Etiene/BMONS/doc/RapportFinal/images/choixArduino.pdf

carte | ADC | nb pin | GSM | processeur | prix | Avantages | Inconvénients
APF28 | 2MHz | 2x80 | Apw | 454MHz | 55 €+ 164€(apw) | ADC rapide | Soudures a effectuer
arduino Mega | 10 kHz | 55(gpio) 16(analog) | shield (57€) | 16MHz | 58€ +57€(shield) | librairie fft disponible | pas de GPS avec ce shield
arduino Due | 1MHz | 54 gpio 12 analog | shield(57€) | 64MHz | 49€+57€(shield) | ADC rapide | pas de librairie fft
netduino | 30MHz | 6 analog 22 gpio | intégré | 120MHz | 30 € | TCP/IP déjà integré ADC rapide | pas commun, 0°C mini, timming?, besoin de beaucoup de memoire
