Etiene/BMONS/doc/RapportFinal/images/specif_comp.pdf

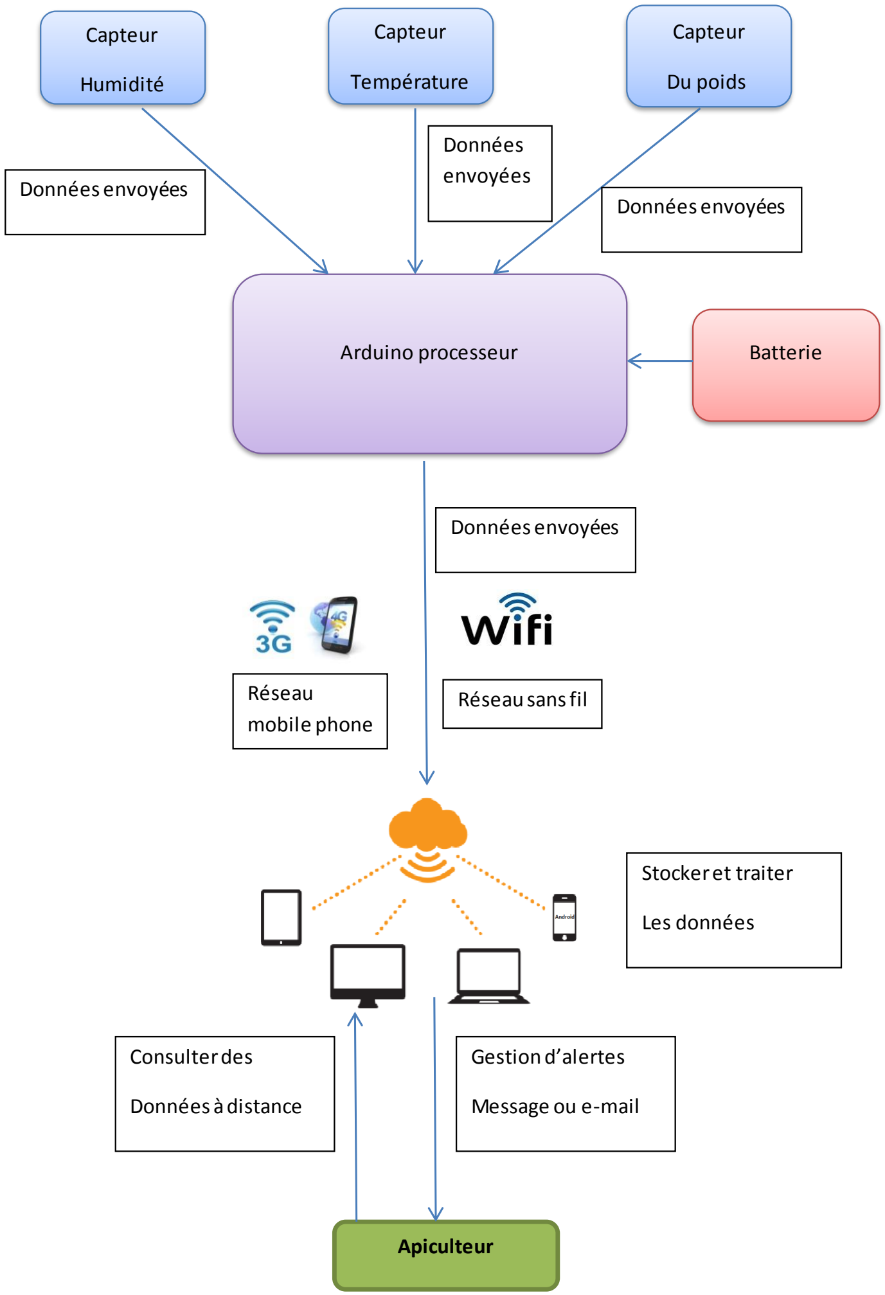
[picture p31: figure]
Capteur; Température; Humidité; Du poids; Apiculteur; Gestion d’alertes; Message ou e-mail; Arduino processeur; Réseau; Réseau sans fil; mobile phone; Données envoyées; Stocker et traiter; Les données; Consulter des; Données à distance; Batterie

Capteur

Système
embarqué

Réseau de
transmission
des données

Utilisateurs

Serveur
