Etiene/BMONS/doc/RapportFinal/images/axeData2.pdf

Bee_Monitor | Alerte Météorologique

Forte pluie, température
inhabituelle (vent ?) qui affectent l'activité/la production
Sources | Requete | Type info
Serveur | Accéder aux données décrivant l'état de sa ruche | Données/Alertes
Sources | Evènement | Element(s) concernés | Remarques
Bee_monitor | Alerte Capteurs endomagés ou mauvaises saisies des données | Ensemble des capteurs | Pour repérer: fortes variations ou valeurs hors intervalles prévus
Sources | Requete | Type info
Serveur | Accéder aux données décrivant l'état de sa ruche | Données/Alertes
Serveur | Configurer | Données/Alertes
Sources | Evènement
Capteur d'inclinaison | Renversement de la ruche
Bee_monitor | Alerte Ruche renversée
Capteur d'ouverture | Couvercle mal placé ou tombé
Bee_monitor | Alerte Ruche ouverte

Transmettre des messages

Alerter l'apiculteur

### FS3: Résister à l'environnement extérieur

Transmettre des messages

Alerter l'apiculteur

### FC2: Résister à l'environement de la ruche
