Etiene/BMONS/doc/RapportFinal/images/axeData3.pdf

Capteur d'inclinaison | Renversement de la ruche
Bee_monitor | Alerte La ruche a subit un choc
Capteur d'humidité | Infiltration/problèmes d'étanchéité
Bee_monitor | Alerte Ruche exposée à l'humidité
Balance | Déplacement de la ruche non prévu
Bee_monitor | Alerte Ruche déplacée
Sources | Data | Unité
Panneaux solaires/Eoliennes | Luminosité reçue/vitesse du vent | Lux-m/s
Batteries du bee_monitor | Energie disponible et consommation | J
Sources | Requete | Type info
Serveur | Accéder aux données décrivant l'état de sa ruche | Données des batteries/Autonomie/Alertes
Serveur | Configurer | Données des batteries/Alertes
Sources | Evènement
Bee_monitor | Alerte Etat des batteries faible

### FS4: Etre autonome en énergie

Alerter l'apiculteur

Transmettre des messages
