Etiene/BMONS/doc/RapportFinal/images/Exigences3.pdf

Transmettre les données par ondes radio | 3G ou 4G

Pouvoir stocker les données localement

Déclancher des mesures à intervalles réguliers

exi met 6 | detecter l'essaimage | Avertir l'apiculteur en cas de détection d'essaimage
| | Mesurer le poids de la ruche | [0 ; 150] résolution 100g fréquence 1/heure
| | Transmettre les données par ondes radio | 3G ou 4G
| | pouvoir stocker les données localement
| | Déclancher des mesures à intervalles réguliers
| | detecter les renversements
| | detecter l'ouverture de la ruche
| | donner la position de la ruche
| | Avertir l'apiculteur en cas de choc
| | Détecter la position de la ruche
| | Transmettre les données par ondes radio | 3G ou 4G
| | Pouvoir stocker les données localement

exi met 7

veiller à la
sécurité de la
ruche

exi met 5

detecter les
premise de
l'essaimage
