Etiene/BMONS/doc/RapportFinal/images/BeteACornesBMONS.pdf

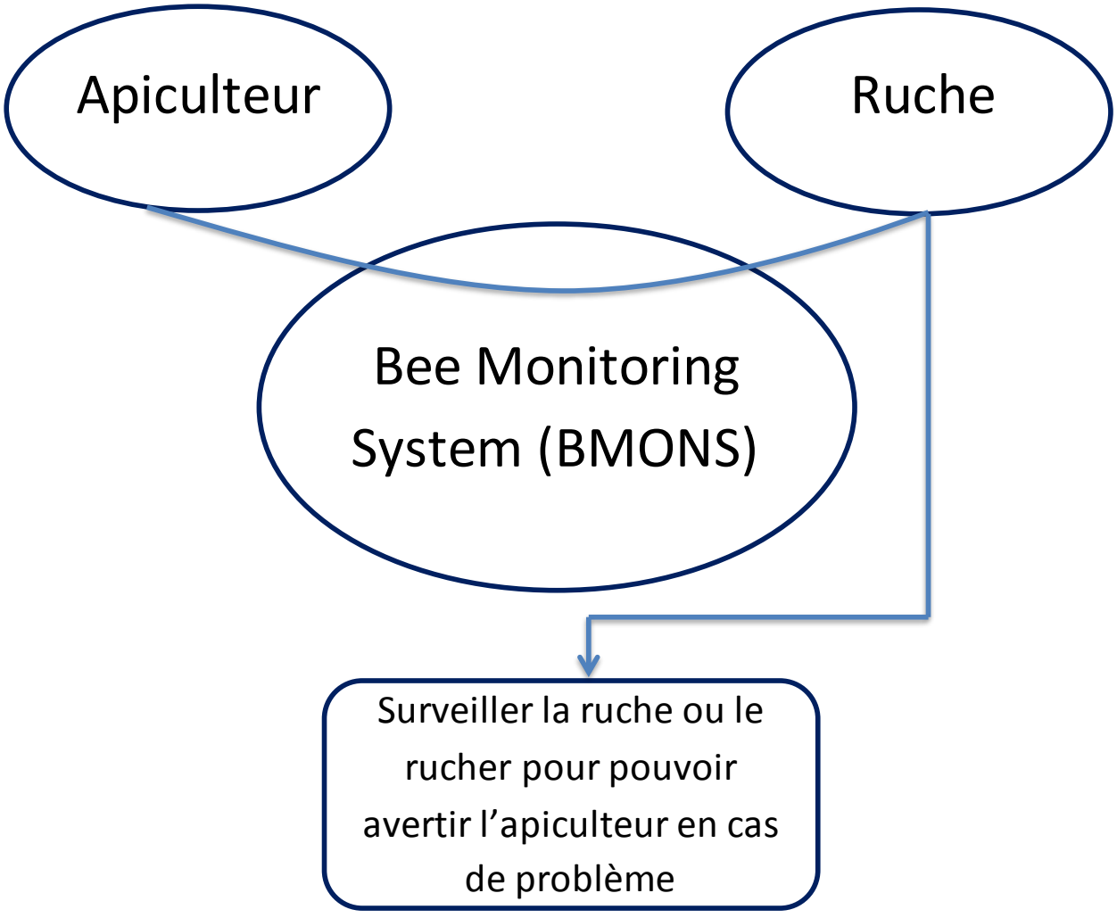
[picture p115: figure]
Surveiller la ruche ou le rucher pour pouvoir avertir l’apiculteur en cas de problème; Ruche; Bee Monitoring System (BMONS); Apiculteur
