Etiene/BMONS/doc/RapportFinal/images/diagpieuvre.pdf

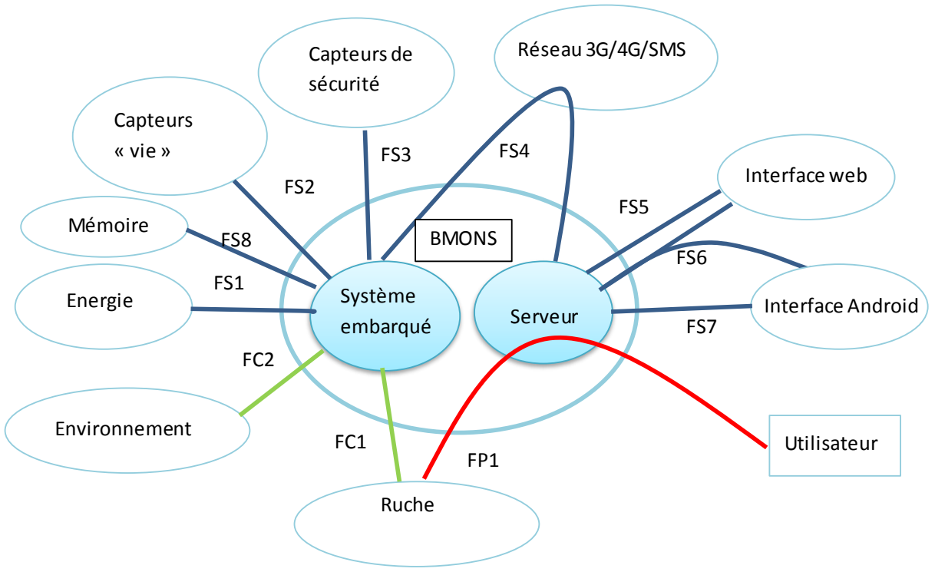
[picture p116: figure]
Capteurs de sécurité; Energie; Environnement; Utilisateur; Interface web; Capteurs « vie »; Réseau 3G/4G/SMS; Système; embarqué; Serveur; Ruche; BMONS; Interface Android; Mémoire

FP1 : Informer l’apiculteur de l’état de la ruche

FC1 : Etre adapté aux dimensions de la ruche FC2 : Résister à l’environnement de la ruche

FS1 : Etre autonome en énergie
FS2 : Acquérir les données relatives à la vie de la ruche
FS3 : Acquérir les données relatives à l’intégrité de la ruche FS4 : Communiquer avec le serveur via le réseau 3G/4G/SMS FS5 : Proposer une IHM web
FS6 : Proposer un accès via l’API
FS7 : Proposer une IHM Android
FS8 : Conserver les données localement
