Etiene/BMONS/doc/FAST.png

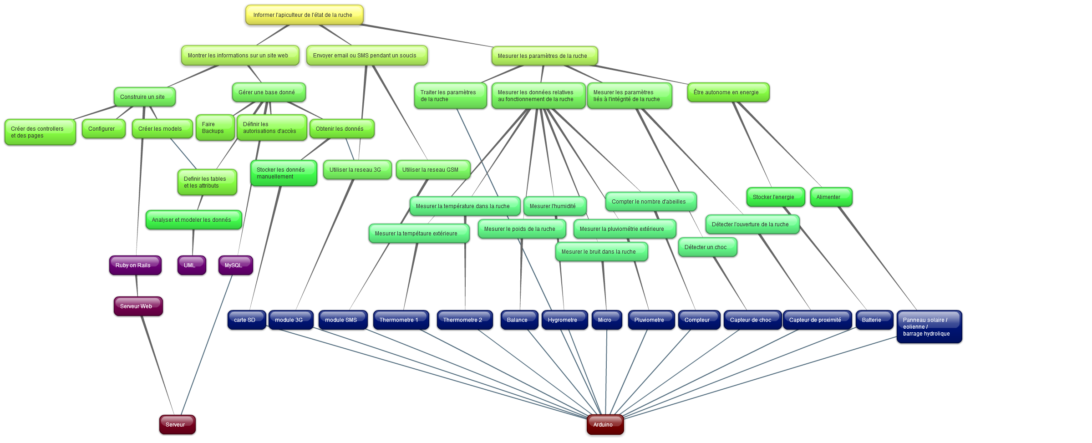
doc/FAST.png
