Etiene/BMONS/doc/Modèle Base de données/digClass.png

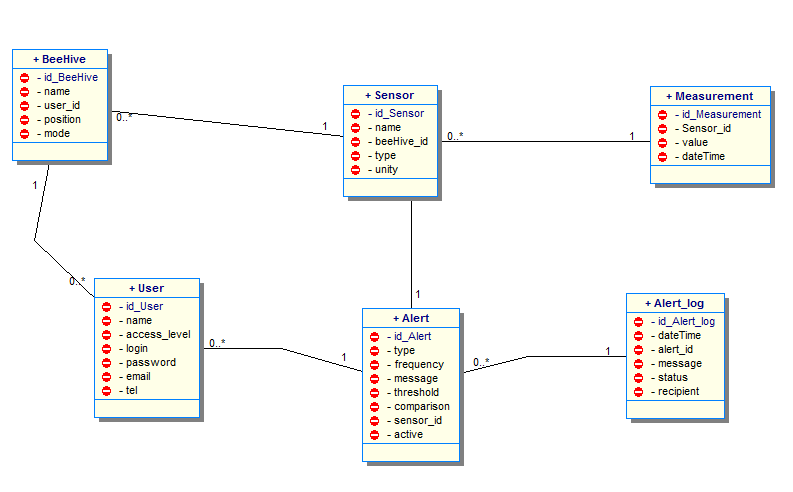
doc/Modèle Base de données/digClass.png
