Etiene/BMONS/doc/Modèle Base de données/mcd.png

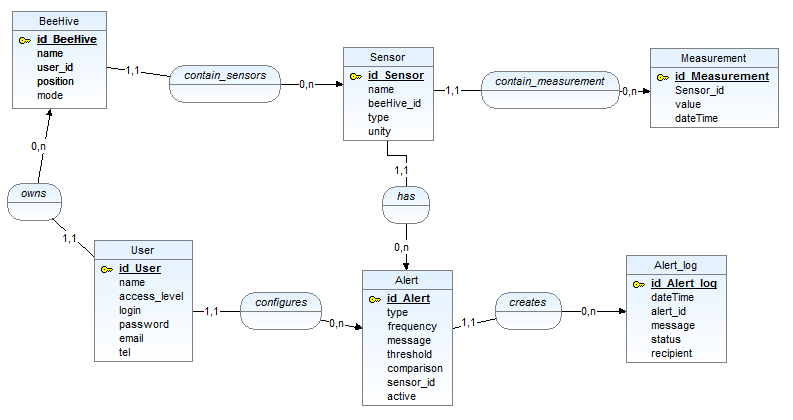
doc/Modèle Base de données/mcd.png
