Etiene/BMONS/doc/Modèle Base de données/MLD.png

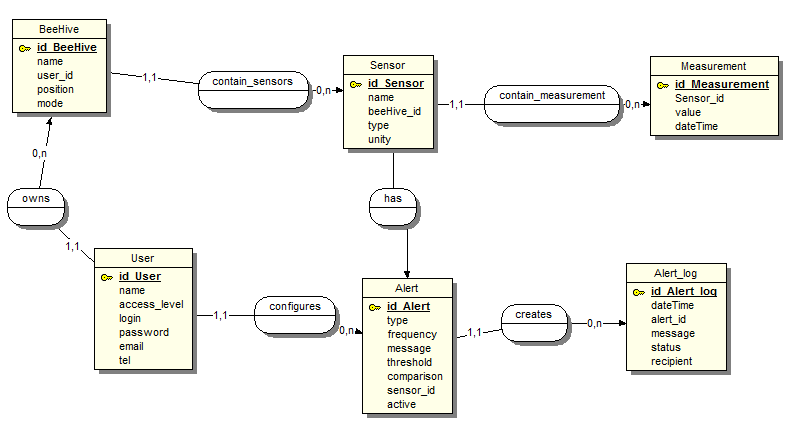
doc/Modèle Base de données/MLD.png
