Etiene/BMONS/doc/RapportFinal/images/arnia2.jpg

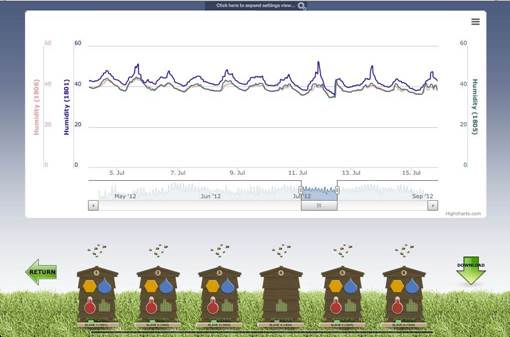
doc/RapportFinal/images/arnia2.jpg
