Etiene/BMONS/doc/RapportFinal/images/GANTT2.png

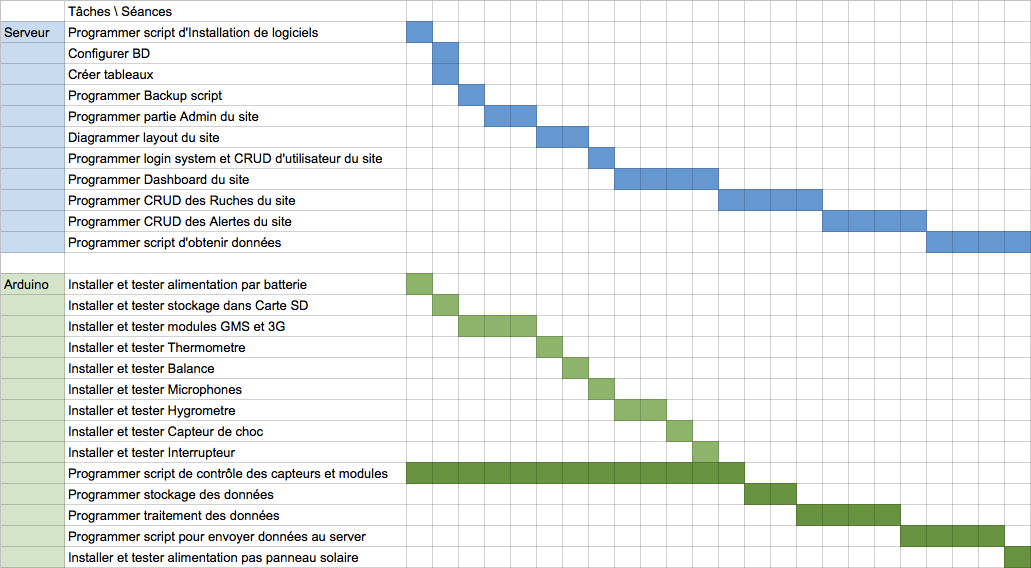
doc/RapportFinal/images/GANTT2.png
