Etiene/BMONS/doc/RapportFinal/images/GANTT.png

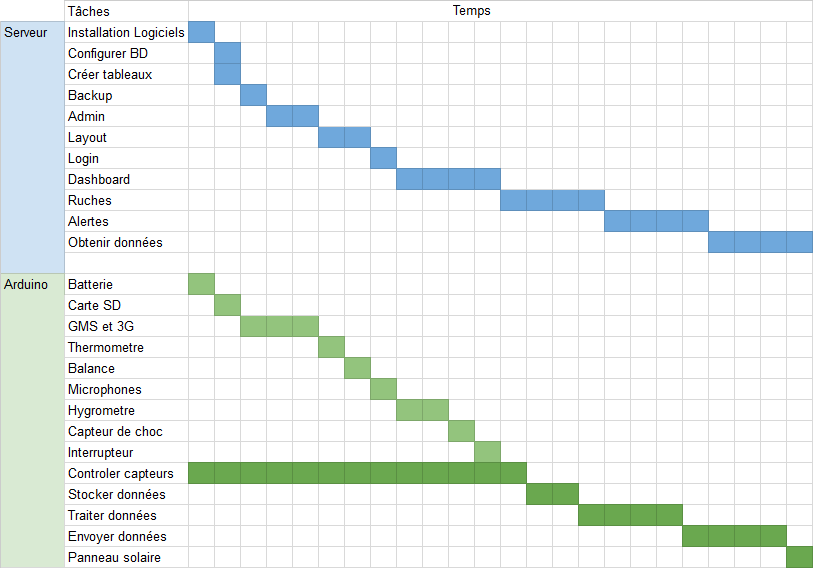
doc/RapportFinal/images/GANTT.png
