Etiene/BMONS/doc/RapportFinal/images/WBS2.png

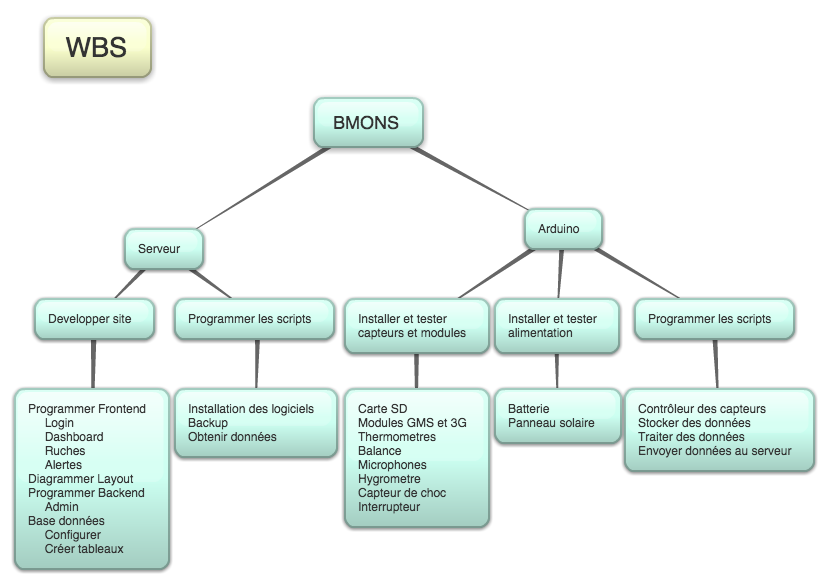
doc/RapportFinal/images/WBS2.png
