Etiene/BMONS/doc/UseCaseDiagram1.jpg

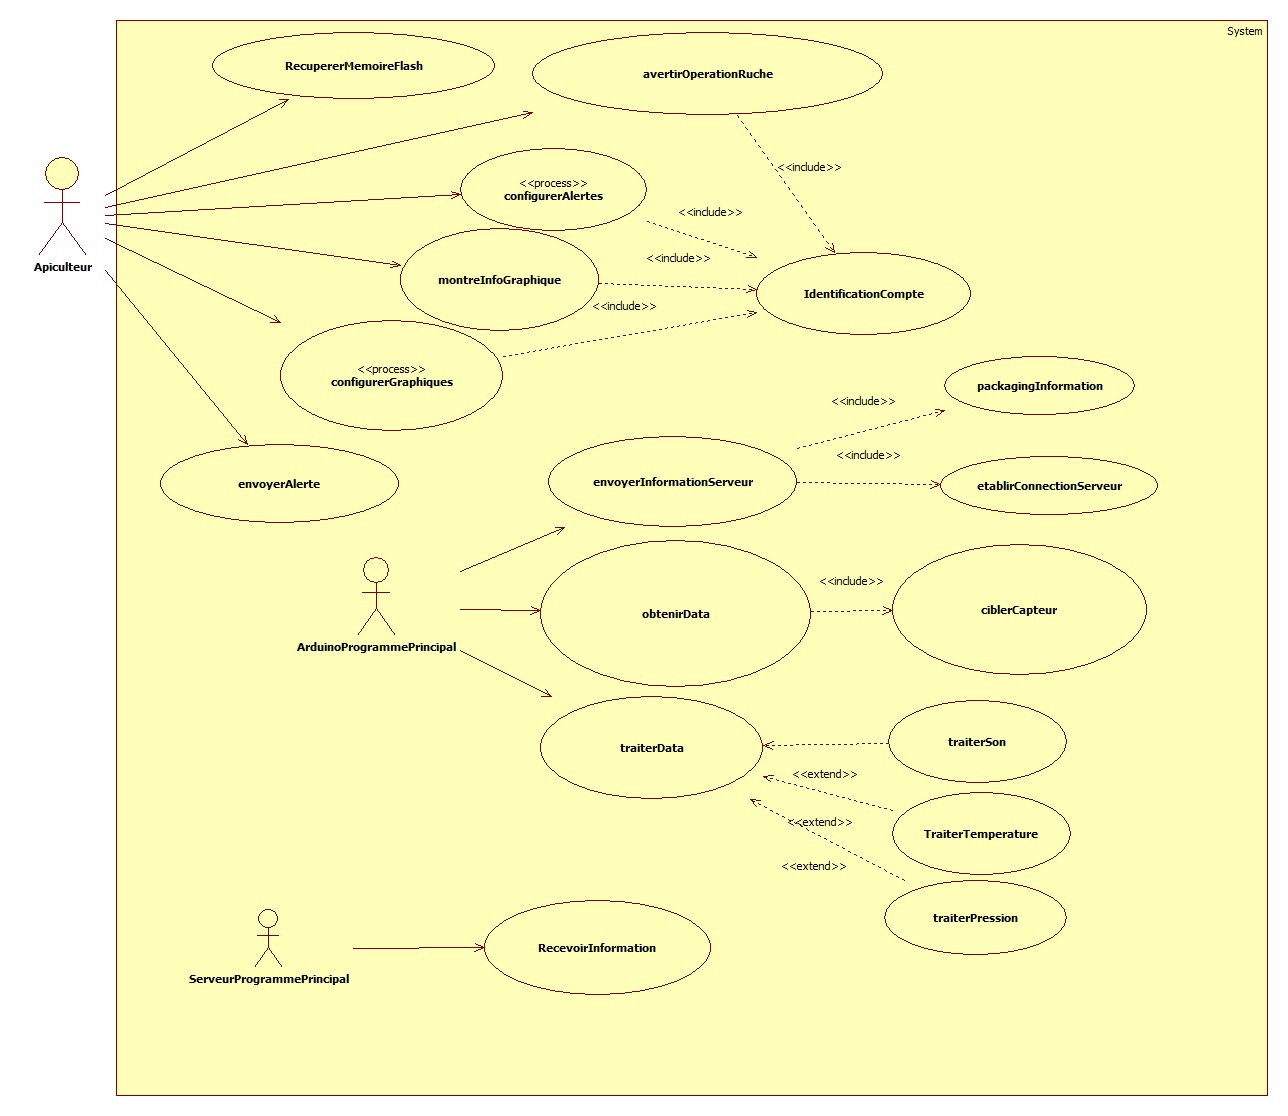
doc/UseCaseDiagram1.jpg
