Etiene/BMONS/doc/UseCaseDiagram2.jpg

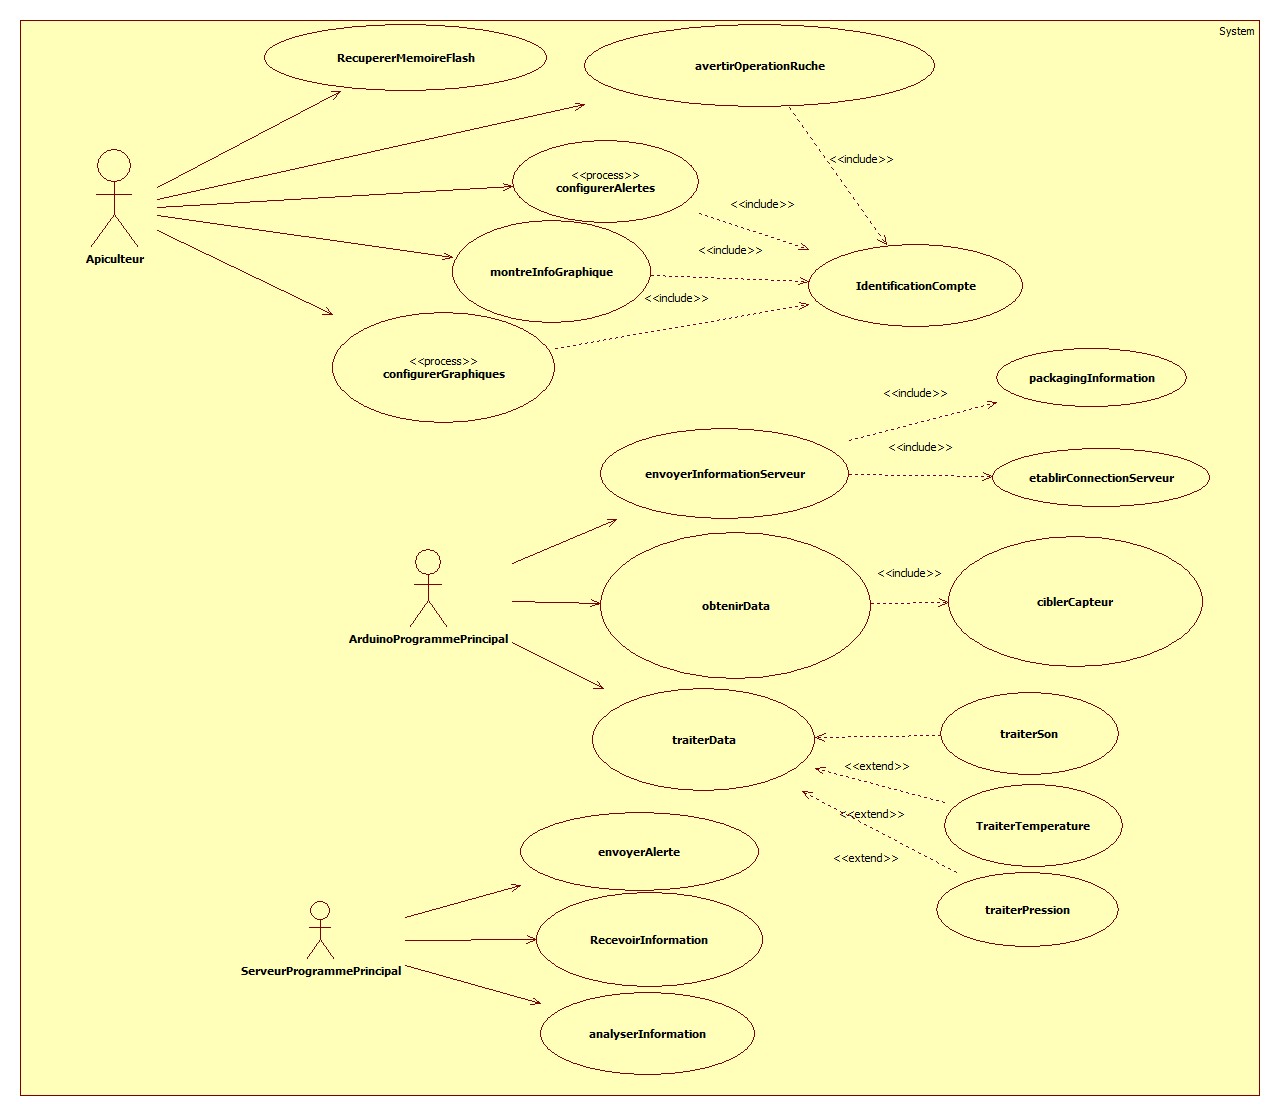
doc/UseCaseDiagram2.jpg
