Etiene/BMONS/doc/RapportFinal/images/ExempleCarnetDeBord.PNG

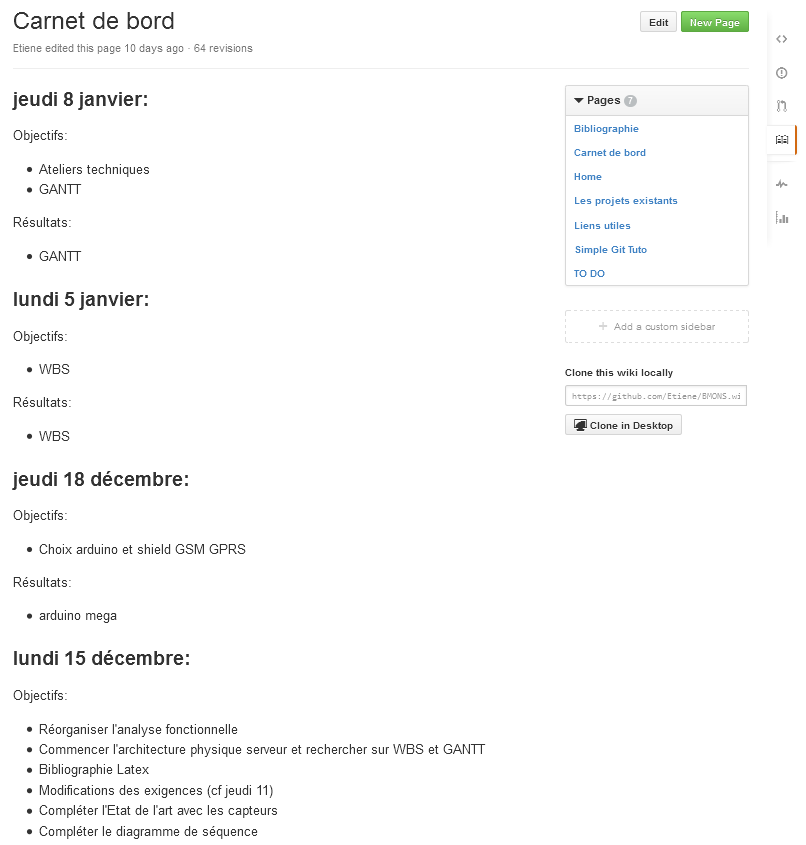
doc/RapportFinal/images/ExempleCarnetDeBord.PNG
