Etiene/BMONS/doc/RapportFinal/images/analyseFonctionelle1.pdf

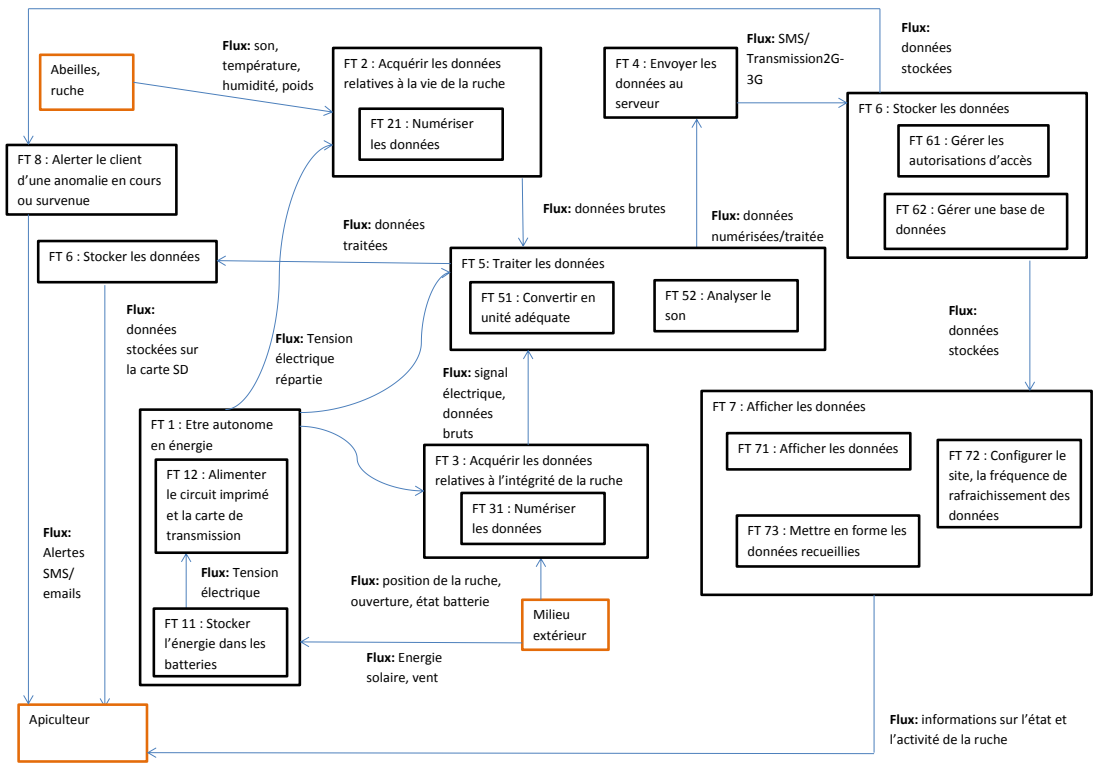
[picture p143: page 1]
Flux: Tension électrique répartie; Flux: Tension électrique; Flux: données stockées; Flux: SMS/ Transmission2G- 3G; Flux: données numérisées/traitée; Flux: son, température, humidité, poids; Flux: données traitées; Milieu extérieur; Apiculteur; Abeilles, ruche; Flux: Energie solaire, vent; FT 21 : Numériser les données; Flux: Alertes SMS/ emails; FT 31 : Numériser les données

FT 2 : Acquérir les données
relatives à la vie de la ruche

FT 4 : Envoyer les
données au
serveur

FT 6 : Stocker les données

FT 61 : Gérer les
autorisations d’accès

FT 8 : Alerter le client
d’une anomalie en cours
ou survenue

Flux: données brutes

FT 62 : Gérer une base de
données

FT 5: Traiter les données

FT 51 : Convertir en
unité adéquate

FT 52 : Analyser le
son

Flux:
stockées sur
la carte SD

Flux: signal
électrique,
bruts
FT 3 : Acquérir les données
relatives à l’intégrité de la ruche

FT 7 : Afficher les données

FT 1 : Etre autonome
en énergie

FT 71 : Afficher les données

FT 72 : Configurer le
site, la fréquence de
rafraichissement des

FT 12 : Alimenter
le circuit imprimé
et la carte de
transmission

FT 73 : Mettre en forme les
données recueillies

Flux: position de la ruche,
ouverture, état batterie

FT 11 : Stocker
l’énergie dans les
batteries

Flux: informations sur l’état et
l’activité de la ruche
