Etiene/BMONS/doc/RapportFinal/images/analyseFonctionelle.pdf

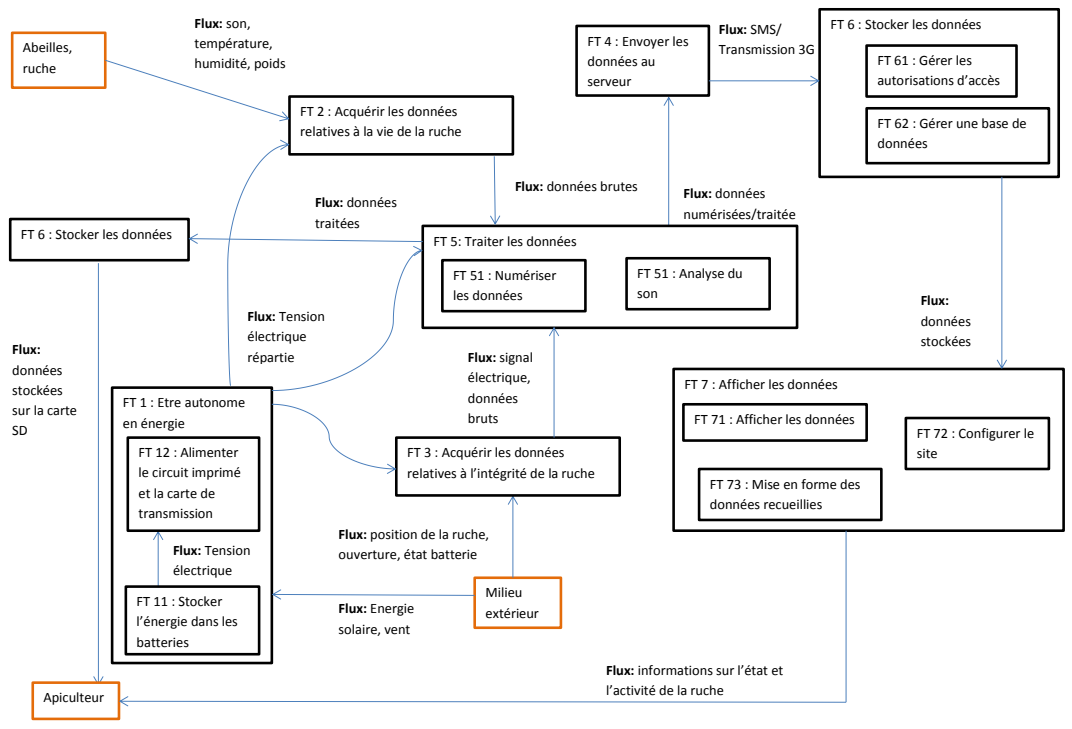
[picture p144: page 1]
Flux: Tension électrique; Flux: données stockées; Flux: SMS/ Transmission 3G; Flux: données numérisées/traitée; Flux: signal électrique, données bruts; Flux: son, température, humidité, poids; Flux: données traitées; Milieu extérieur; Apiculteur; Abeilles, ruche; Flux: Energie solaire, vent; FT 51 : Numériser les données

FT 6 : Stocker les données

FT 4 : Envoyer les
données au
serveur

FT 61 : Gérer les
autorisations d’accès

FT 2 : Acquérir les données
relatives à la vie de la ruche

FT 62 : Gérer une base de
données

Flux: données brutes

FT 5: Traiter les données

FT 51 : Analyse du
son

répartie Flux:
stockées
sur la carte

FT 7 : Afficher les données

FT 1 : Etre autonome
en énergie

FT 71 : Afficher les données

FT 72 : Configurer le
site

FT 12 : Alimenter
le circuit imprimé
et la carte de
transmission

FT 3 : Acquérir les données
relatives à l’intégrité de la ruche

FT 73 : Mise en forme des
données recueillies

Flux: position de la ruche,
ouverture, état batterie

FT 11 : Stocker
l’énergie dans les
batteries

Flux: informations sur l’état et
l’activité de la ruche
