Etiene/BMONS/doc/Fast_BMONS.pdf

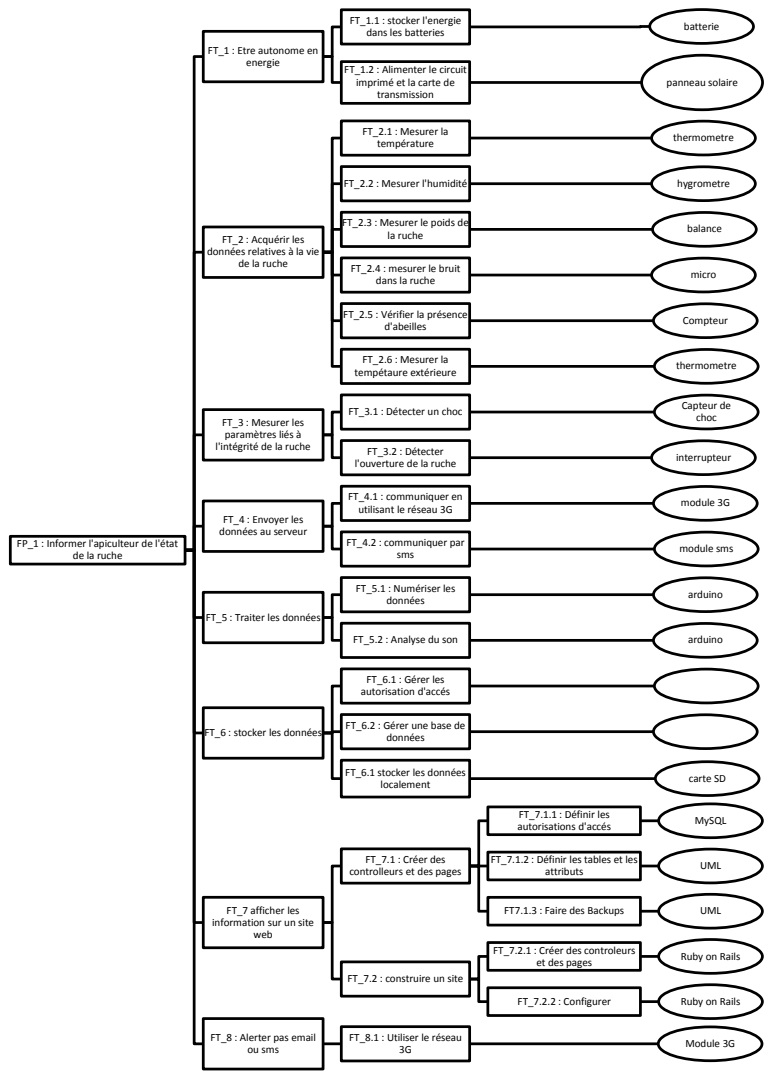
[picture p145: page 1]
energie; FT_1.1 : stocker l'energie; dans les batteries; batterie; panneau solaire; FT_2.1 : Mesurer la; température; thermometre; FT_2.2 : Mesurer l'humidité; hygrometre; la ruche; balance; dans la ruche; micro; d'abeilles; Compteur; FT_2.6 : Mesurer la; tempétaure extérieure; FT_3.1 : Détecter un choc; Capteur de; choc; FT_3.2 : Détecter; l'ouverture de la ruche; interrupteur; FT_4.1 : communiquer en; utilisant le réseau 3G; module 3G; FT_4.2 : communiquer par sms; module sms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

FT_1 : Etre autonome en

FT_1.2 : Alimenter le circuit
imprimé et la carte de
transmission

FT_2.3 : Mesurer le poids de

FT_2 : Acquérir les
données relatives à la vie
de la ruche

FT_2.4 : mesurer le bruit

FT_2.5 : Vérifier la présence

FT_3 : Mesurer les
paramètres liés à
l'intégrité de la ruche

FT_4 : Envoyer les
données au serveur

FP_1 : Informer l'apiculteur de l'état

FT_5 : Traiter les données

FT_6.2 : Gérer une base de

FT_6 : stocker les données

FT_6.1 stocker les données

FT_7.1 : Créer des
controlleurs et des pages

FT_7.1.2 : Définir les tables et les

FT_7 afficher les
information sur un site

FT_7.2.1 : Créer des controleurs

FT_7.2 : construire un site

FT_8 : Alerter pas email

FT_8.1 : Utiliser le réseau
