Etiene/BMONS/bmons-site/test/fixtures/measurements.yml

# Read about fixtures at http://api.rubyonrails.org/classes/ActiveRecord/FixtureSet.html

#TEMPERATURE RUCHE 1
one:
  value: 15
  datetime: 2015-02-17 17:05:09
  sensor_id: 1

two:
  value: 15.1
  datetime: 2015-02-17 17:15:09
  sensor_id: 1

three:
  value: 15.2
  datetime: 2015-02-17 17:25:09
  sensor_id: 1

four:
  value: 15.3
  datetime: 2015-02-17 17:35:09
  sensor_id: 1

five:
  value: 16
  datetime: 2015-02-17 17:45:09
  sensor_id: 1

six:
  value: 15.3
  datetime: 2015-02-17 17:55:09
  sensor_id: 1

seven:
  value: 15
  datetime: 2015-02-17 18:05:09
  sensor_id: 1

eight:
  value: 15.1
  datetime: 2015-02-17 18:15:09
  sensor_id: 1

nine:
  value: 15
  datetime: 2015-02-17 18:25:09
  sensor_id: 1

ten:
  value: 14.8
  datetime: 2015-02-17 18:35:09
  sensor_id: 1

one2:
  value: 14.6
  datetime: 2015-02-17 18:45:09
  sensor_id: 1

two2:
  value: 14.4
  datetime: 2015-02-17 18:55:09
  sensor_id: 1

three2:
  value: 14.2
  datetime: 2015-02-17 19:05:09
  sensor_id: 1

four2:
  value: 14
  datetime: 2015-02-17 19:15:09
  sensor_id: 1

five2:
  value: 13.8
  datetime: 2015-02-17 19:25:09
  sensor_id: 1

six2:
  value: 13.6
  datetime: 2015-02-17 19:35:09
  sensor_id: 1

seven2:
  value: 13.4
  datetime: 2015-02-17 19:45:09
  sensor_id: 1

eight2:
  value: 13.2
  datetime: 2015-02-17 19:55:09
  sensor_id: 1

nine2:
  value: 13
  datetime: 2015-02-17 20:05:09
  sensor_id: 1

ten2:
  value: 13
  datetime: 2015-02-17 20:15:09
  sensor_id: 1

one3:
  value: 13.5
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
  sensor_id: 2

seven12:
  value: 1.2
  datetime: 2015-02-17 23:05:09
  sensor_id: 2

eight12:
  value: 1.3
  datetime: 2015-02-17 23:15:09
  sensor_id: 2

nine12:
  value: 1.3
  datetime: 2015-02-17 23:25:09
  sensor_id: 2

ten12:
  value: 1.4
  datetime: 2015-02-17 23:35:09
  sensor_id: 2
